murmure-0/Car-Camera-Shutter-Alert/3d_model_assets/锁扣公头.SLDPRT

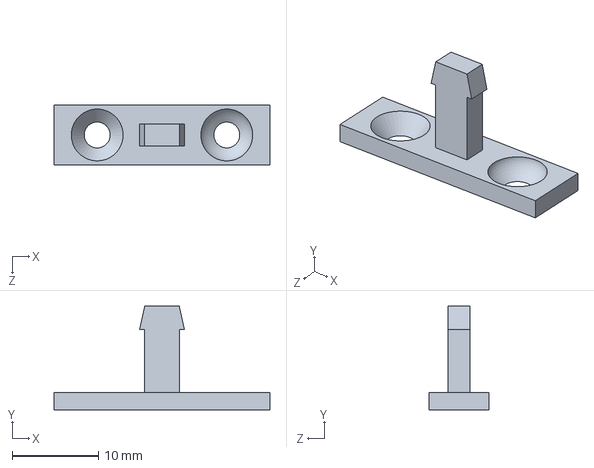
[picture p17: CAD file, 2026-05-22]
3d_model_assets/锁扣公头.SLDPRT
25.0 x 12.0 x 7.00 mm
