murmure-0/Car-Camera-Shutter-Alert/3d_model_assets/摄像头.SLDPRT

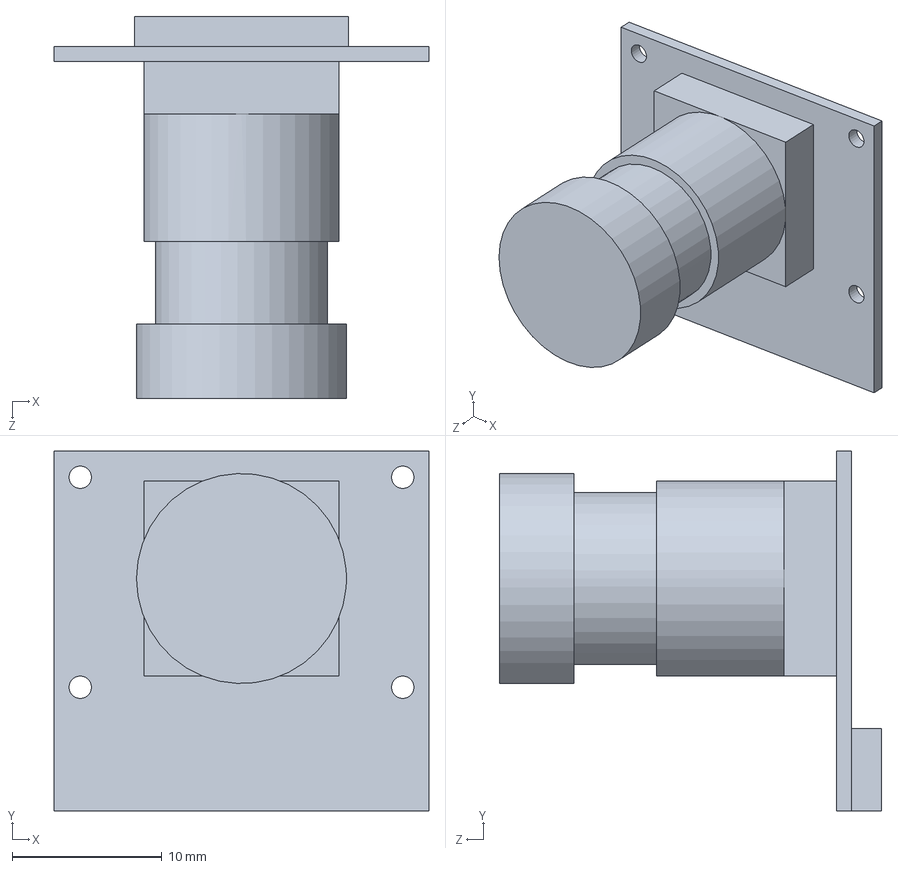
[picture p18: CAD file, 2026-05-22]
3d_model_assets/摄像头.SLDPRT
25.0 x 24.0 x 25.5 mm
