murmure-0/Car-Camera-Shutter-Alert/3d_model_assets/右盖板.SLDPRT

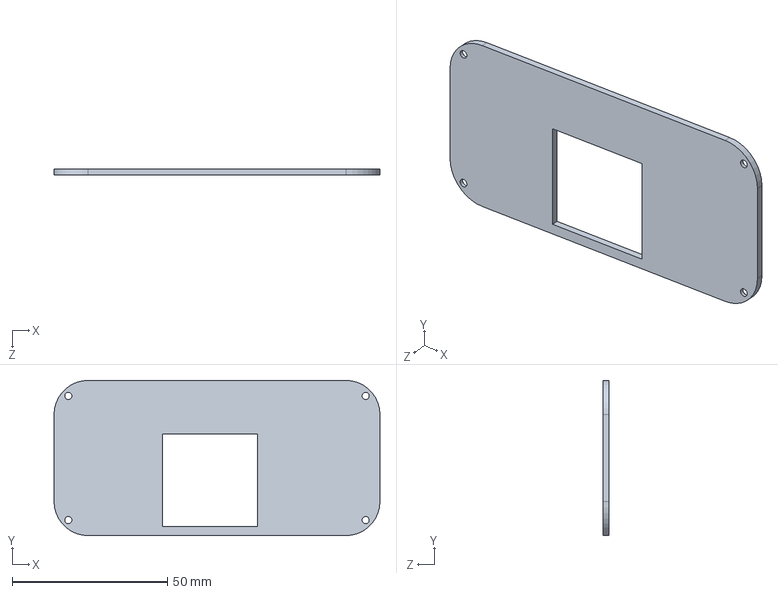
[picture p19: CAD file, 2026-05-22]
3d_model_assets/右盖板.SLDPRT
105.0 x 50.0 x 2.00 mm
