murmure-0/Car-Camera-Shutter-Alert/3d_model_assets/GB／T283-94圆柱滚子轴承NH202E.SLDPRT

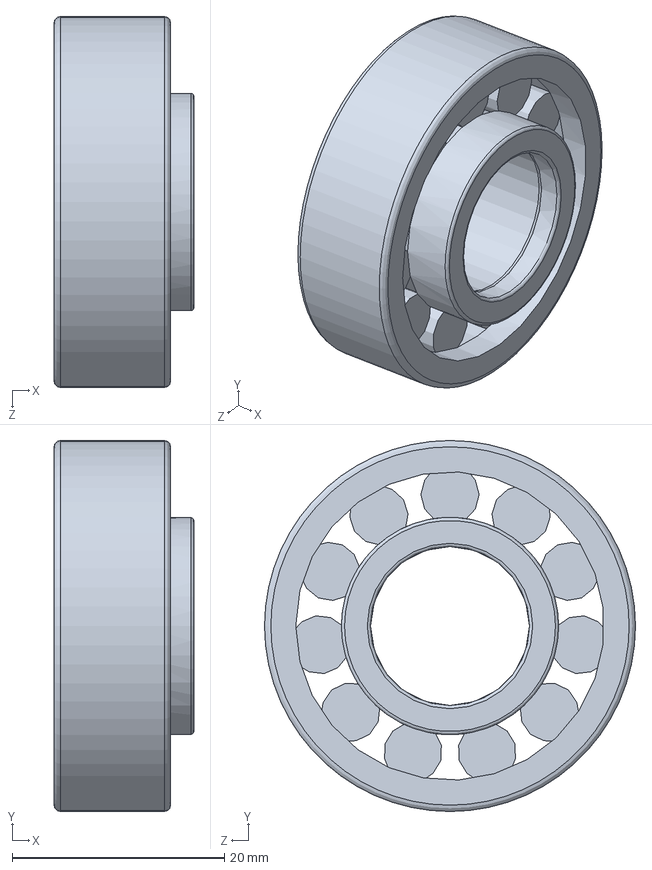
[picture p20: CAD file, 2026-05-22]
3d_model_assets/GB／T283-94圆柱滚子轴承NH202E.SLDPRT
13.2 x 35.0 x 35.0 mm
