murmure-0/Car-Camera-Shutter-Alert/3d_model_assets/LED驱动板.SLDPRT

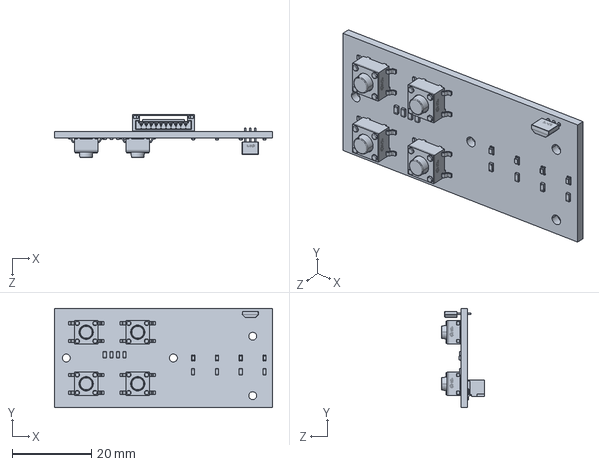
[picture p21: CAD file, 2026-05-22]
3d_model_assets/LED驱动板.SLDPRT
55.0 x 25.0 x 11.0 mm
