murmure-0/Car-Camera-Shutter-Alert/rv1106_sensor/Core/Inc/usart1_handler.h

#ifndef __USART1_HANDLER_H
#define __USART1_HANDLER_H

#ifdef __cplusplus
extern "C" {
#endif

#include "main.h"

/* USART1处理任务 */
void Usart1Handler_Task(void const *argument);

#ifdef __cplusplus
}
#endif

#endif /* __USART1_HANDLER_H */
