murmure-0/Car-Camera-Shutter-Alert/qt_car_ui/camera/luckfox_mpi.cc

/*****************************************************************************
* | Author      :   Luckfox team
* | Function    :   
* | Info        :
*
*----------------
* | This version:   V1.0
* | Date        :   2024-04-07
* | Info        :   Basic version
*
******************************************************************************/

#include "luckfox_mpi.h"

// 获取单调递增时钟的微秒时间戳
RK_U64 TEST_COMM_GetNowUs() {
	struct timespec time = {0, 0};
	clock_gettime(CLOCK_MONOTONIC, &time);
	return (RK_U64)time.tv_sec * 1000000 + (RK_U64)time.tv_nsec / 1000; /* microseconds */
}

// 初始化 VI 设备：配置设备属性、启用设备、绑定到 pipe
int vi_dev_init() {
	printf("%s\n", __func__);
	int ret = 0;
	int devId = 0;
	int pipeId = devId;

	VI_DEV_ATTR_S stDevAttr;
	VI_DEV_BIND_PIPE_S stBindPipe;
	memset(&stDevAttr, 0, sizeof(stDevAttr));
	memset(&stBindPipe, 0, sizeof(stBindPipe));
	// 0. get dev config status
	ret = RK_MPI_VI_GetDevAttr(devId, &stDevAttr);
	if (ret == RK_ERR_VI_NOT_CONFIG) {
		// 0-1.config dev
		ret = RK_MPI_VI_SetDevAttr(devId, &stDevAttr);
		if (ret != RK_SUCCESS) {
			printf("RK_MPI_VI_SetDevAttr %x\n", ret);
			return -1;
		}
	} else {
		printf("RK_MPI_VI_SetDevAttr already\n");
	}
	// 1.get dev enable status
	ret = RK_MPI_VI_GetDevIsEnable(devId);
	if (ret != RK_SUCCESS) {
		// 1-2.enable dev
		ret = RK_MPI_VI_EnableDev(devId);
		if (ret != RK_SUCCESS) {
			printf("RK_MPI_VI_EnableDev %x\n", ret);
			return -1;
		}
		// 1-3.bind dev/pipe
		stBindPipe.u32Num = pipeId;
		stBindPipe.PipeId[0] = pipeId;
		ret = RK_MPI_VI_SetDevBindPipe(devId, &stBindPipe);
		if (ret != RK_SUCCESS) {
			printf("RK_MPI_VI_SetDevBindPipe %x\n", ret);
			return -1;
		}
	} else {
		printf("RK_MPI_VI_EnableDev already\n");
	}

	return 0;
}

// 初始化 VI 通道：设置图像尺寸、像素格式与缓冲策略
int vi_chn_init(int channelId, int width, int height) {
	int ret;
	int buf_cnt = 2;
	// VI init
	VI_CHN_ATTR_S vi_chn_attr;
	memset(&vi_chn_attr, 0, sizeof(vi_chn_attr));
	vi_chn_attr.stIspOpt.u32BufCount = buf_cnt;
	vi_chn_attr.stIspOpt.enMemoryType =
	    VI_V4L2_MEMORY_TYPE_DMABUF; // VI_V4L2_MEMORY_TYPE_MMAP;
	vi_chn_attr.stSize.u32Width = width;
	vi_chn_attr.stSize.u32Height = height;
	vi_chn_attr.enPixelFormat = RK_FMT_YUV420SP;
	vi_chn_attr.enCompressMode = COMPRESS_MODE_NONE; // COMPRESS_AFBC_16x16;
	vi_chn_attr.u32Depth = 2;
	ret = RK_MPI_VI_SetChnAttr(0, channelId, &vi_chn_attr);
	ret |= RK_MPI_VI_EnableChn(0, channelId);
	if (ret) {
		printf("ERROR: create VI error! ret=%x\n", ret);
		return ret;
	}

	return ret;
}

// 初始化 VPSS：创建组、配置通道、开启 VPSS 处理链
int vpss_init(int VpssChn, int width, int height) {
	printf("%s\n",__func__);
	int s32Ret;
	VPSS_CHN_ATTR_S stVpssChnAttr;
	VPSS_GRP_ATTR_S stGrpVpssAttr;

	int s32Grp = 0;

	stGrpVpssAttr.u32MaxW = 4096;
	stGrpVpssAttr.u32MaxH = 4096;
	stGrpVpssAttr.enPixelFormat = RK_FMT_YUV420SP;
	stGrpVpssAttr.stFrameRate.s32SrcFrameRate = -1;
	stGrpVpssAttr.stFrameRate.s32DstFrameRate = -1;
	stGrpVpssAttr.enCompressMode = COMPRESS_MODE_NONE;

	stVpssChnAttr.enChnMode = VPSS_CHN_MODE_USER;
	stVpssChnAttr.enDynamicRange = DYNAMIC_RANGE_SDR8;
	stVpssChnAttr.enPixelFormat = RK_FMT_RGB888;
	stVpssChnAttr.stFrameRate.s32SrcFrameRate = -1;
	stVpssChnAttr.stFrameRate.s32DstFrameRate = -1;
	stVpssChnAttr.u32Width = width;
	stVpssChnAttr.u32Height = height;
	stVpssChnAttr.enCompressMode = COMPRESS_MODE_NONE;

	s32Ret = RK_MPI_VPSS_CreateGrp(s32Grp, &stGrpVpssAttr);
	if (s32Ret != RK_SUCCESS) {
		return s32Ret;
	}

	s32Ret = RK_MPI_VPSS_SetChnAttr(s32Grp, VpssChn, &stVpssChnAttr);
	if (s32Ret != RK_SUCCESS) {
		return s32Ret;
	}
	s32Ret = RK_MPI_VPSS_EnableChn(s32Grp, VpssChn);
	if (s32Ret != RK_SUCCESS) {
		return s32Ret;
	}

	s32Ret = RK_MPI_VPSS_StartGrp(s32Grp);
	if (s32Ret != RK_SUCCESS) {
		return s32Ret;
	}
	return s32Ret;
}

// 初始化编码器：配置 H264 码流参数并开始接收帧
int venc_init(int chnId, int width, int height, RK_CODEC_ID_E enType) {
	printf("%s\n",__func__);
	VENC_RECV_PIC_PARAM_S stRecvParam;
	VENC_CHN_ATTR_S stAttr;
	memset(&stAttr, 0, sizeof(VENC_CHN_ATTR_S));

	// RTSP H264
	stAttr.stVencAttr.enType = enType;
	//stAttr.stVencAttr.enPixelFormat = RK_FMT_YUV420SP;
	stAttr.stVencAttr.enPixelFormat = RK_FMT_RGB888;	
	stAttr.stVencAttr.u32Profile = H264E_PROFILE_MAIN;
	stAttr.stVencAttr.u32PicWidth = width;
	stAttr.stVencAttr.u32PicHeight = height;
	stAttr.stVencAttr.u32VirWidth = width;
	stAttr.stVencAttr.u32VirHeight = height;
	stAttr.stVencAttr.u32StreamBufCnt = 2;
	stAttr.stVencAttr.u32BufSize = width * height * 3 / 2;
	stAttr.stVencAttr.enMirror = MIRROR_NONE;
		
	stAttr.stRcAttr.enRcMode = VENC_RC_MODE_H264CBR;
	stAttr.stRcAttr.stH264Cbr.u32BitRate = 3 * 1024;
	stAttr.stRcAttr.stH264Cbr.u32Gop = 1;
	RK_MPI_VENC_CreateChn(chnId, &stAttr);

	memset(&stRecvParam, 0, sizeof(VENC_RECV_PIC_PARAM_S));
	stRecvParam.s32RecvPicNum = -1;
	RK_MPI_VENC_StartRecvFrame(chnId, &stRecvParam);

	return 0;
}
