murmure-0/Car-Camera-Shutter-Alert/qt_car_ui/pages/connectivitypage.h

#ifndef CONNECTIVITYPAGE_H
#define CONNECTIVITYPAGE_H

#include <QWidget>

class ConnectivityPage : public QWidget
{
    Q_OBJECT
public:
    explicit ConnectivityPage(QWidget *parent = nullptr);
};

#endif // CONNECTIVITYPAGE_H
